Borek-32/EEE491-Spoken-Digit-Recognizer-BASYS3/hardware/homefab_mic_adc_pcb/kicad/evidence/report_views/pcb_named_nets_top_copper.png

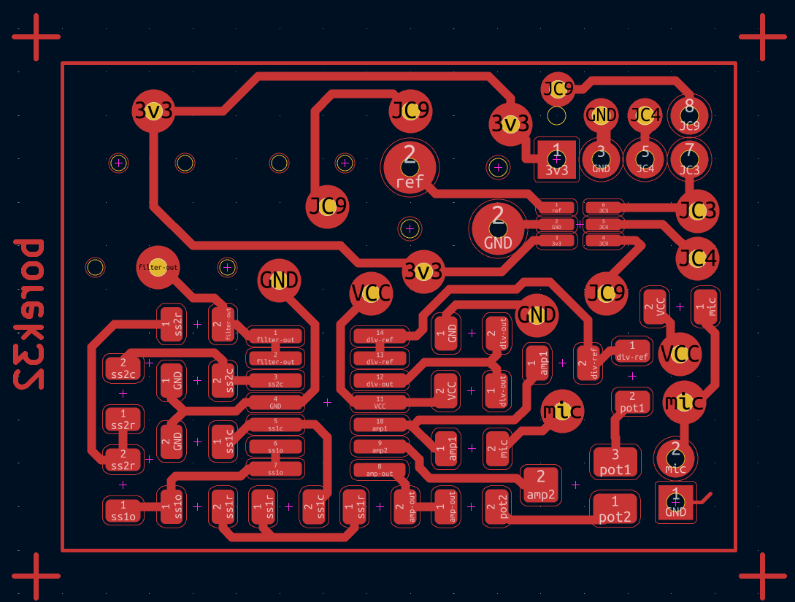
hardware/homefab_mic_adc_pcb/kicad/evidence/report_views/pcb_named_nets_top_copper.png
