Borek-32/EEE491-Spoken-Digit-Recognizer-BASYS3/hardware/homefab_mic_adc_pcb/photos/20260819_190726_operating_on_basys3.jpg

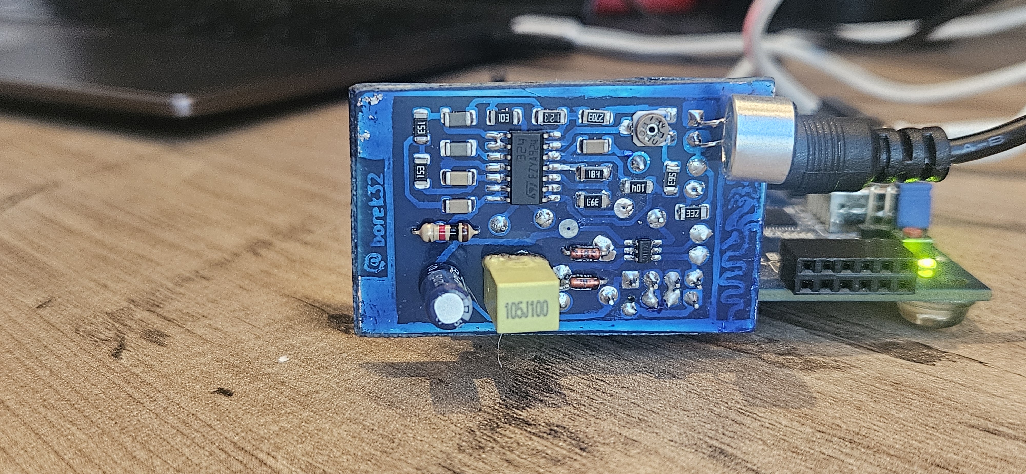
hardware/homefab_mic_adc_pcb/photos/20260819_190726_operating_on_basys3.jpg
