Borek-32/EEE491-Spoken-Digit-Recognizer-BASYS3/testbench/tb_comp.vhd

library IEEE;
use IEEE.STD_LOGIC_1164.ALL;
use IEEE.NUMERIC_STD.ALL;

-- Self-contained COMP testbench generated from verification/last_capture.mat.
-- Offline squared-Euclidean expectation: digit 9, best_ref 27, window_start 7, distance 7771316.
-- Active-start detector: first frame with sum(MEL) > max(sum(MEL))/8. Threshold 67967.
-- The three IP models below replace the Xilinx BRAM/multiplier IPs for behavioral simulation.

package tb_comp_data_pkg is
	type frame8_int_t is array (0 to 7) of integer;
	type capture_dct_t is array (0 to 62) of frame8_int_t;
	constant CAPTURE_DCT : capture_dct_t := (
		 0 => (-473, -228, 478, -880, 539, 43, 189, 385),
		 1 => (54, 77, 494, -702, 392, -226, 182, 308),
		 2 => (1374, 617, 491, -727, 62, -835, -648, -183),
		 3 => (1488, 148, 536, -544, 62, -852, -618, -310),
		 4 => (1300, 229, 81, -625, -103, -1049, -481, -194),
		 5 => (1278, 87, 206, -726, 195, -1331, -400, -251),
		 6 => (1566, -121, 271, -414, 204, -1445, -333, -294),
		 7 => (2195, -1037, -169, -797, 242, -930, -197, -243),
		 8 => (1953, -1395, -442, -644, 136, -942, 276, -369),
		 9 => (1680, -1577, -457, -553, 166, -816, 392, -420),
		10 => (1548, -1683, -520, -454, 272, -743, 436, -479),
		11 => (1387, -1852, -568, -504, 294, -798, 404, -613),
		12 => (1323, -1937, -592, -485, 327, -893, 277, -596),
		13 => (1505, -1901, -499, -424, 368, -787, 291, -405),
		14 => (1414, -1720, -521, -420, 285, -937, 383, -477),
		15 => (1522, -1866, -463, -559, 106, -994, 158, -459),
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
	port (
		clka  : in  std_logic;
		wea   : in  std_logic_vector(0 downto 0);
		addra : in  std_logic_vector(3 downto 0);
		dina  : in  std_logic_vector(127 downto 0);
		clkb  : in  std_logic;
		addrb : in  std_logic_vector(3 downto 0);
		doutb : out std_logic_vector(127 downto 0)
	);
end entity;

architecture sim of blk_mem_gen_comp_window_buf is
	type ram_t is array (0 to 15) of std_logic_vector(127 downto 0);
	signal ram : ram_t := (others => (others => '0'));
begin
	process(clka)
	begin
		if rising_edge(clka) then
			if wea(0) = '1' then
				ram(to_integer(unsigned(addra))) <= dina;
			end if;
		end if;
	end process;

	process(clkb)
	begin
		if rising_edge(clkb) then
			doutb <= ram(to_integer(unsigned(addrb)));
		end if;
	end process;
end architecture;

library IEEE;
use IEEE.STD_LOGIC_1164.ALL;
use IEEE.NUMERIC_STD.ALL;

entity mult_gen_comp_square is
	port (
		CLK : in  std_logic;
		A   : in  std_logic_vector(16 downto 0);
		B   : in  std_logic_vector(16 downto 0);
		P   : out std_logic_vector(33 downto 0)
	);
end entity;

architecture sim of mult_gen_comp_square is
	constant LATENCY : integer := 6;
	type pipe_t is array (0 to LATENCY - 1) of signed(33 downto 0);
	signal pipe : pipe_t := (others => (others => '0'));
begin
	process(CLK)
		variable prod : signed(33 downto 0);
	begin
		if rising_edge(CLK) then
			prod := resize(signed(A) * signed(B), 34);
			pipe(0) <= prod;
			for i in 1 to LATENCY - 1 loop
				pipe(i) <= pipe(i - 1);
			end loop;
			P <= std_logic_vector(pipe(LATENCY - 1));
		end if;
	end process;
end architecture;

library IEEE;
use IEEE.STD_LOGIC_1164.ALL;
use IEEE.NUMERIC_STD.ALL;
use STD.TEXTIO.ALL;
use STD.ENV.ALL;
use work.tb_comp_data_pkg.all;

entity tb_comp is
end entity;

architecture sim of tb_comp is
	constant CLK_PERIOD : time := 10 ns;
	constant DCT_DATA_LATENCY : integer := 3;
	constant MEL_DATA_LATENCY : integer := 3;
	type dct_addr_pipe_t is array (0 to DCT_DATA_LATENCY - 1) of std_logic_vector(2 downto 0);
	type mel_addr_pipe_t is array (0 to MEL_DATA_LATENCY - 1) of std_logic_vector(4 downto 0);
	signal clk          : std_logic := '0';
	signal reset_in     : std_logic := '1';
	signal clear_in     : std_logic := '0';
	signal start_in     : std_logic := '0';
	signal ready_out    : std_logic;
	signal dct_addr_out : std_logic_vector(2 downto 0);
	signal dct_data_in  : std_logic_vector(15 downto 0) := (others => '0');
	signal mel_addr_out : std_logic_vector(4 downto 0);
	signal mel_data_in  : std_logic_vector(31 downto 0) := (others => '0');
	signal selected_digit_in : std_logic_vector(4 downto 0) := "01001";
	signal selected_trial_in : std_logic_vector(2 downto 0) := "000";
	signal mode_record_in : std_logic := '0';
	signal record_out   : std_logic;
	signal flush        : std_logic := '0';
	signal flush_done   : std_logic;
	signal digit_out    : std_logic_vector(3 downto 0);
	signal valid_out    : std_logic;
	signal digit_idx3_patch : std_logic;
	signal frame_idx    : integer range 0 to 62 := 0;
	signal dct_addr_pipe : dct_addr_pipe_t := (others => (others => '0'));
	signal mel_addr_pipe : mel_addr_pipe_t := (others => (others => '0'));
	signal capture_dct_data : capture_dct_t := CAPTURE_DCT;
	signal capture_mel_data : capture_mel_t := CAPTURE_MEL;
begin
	clk <= not clk after CLK_PERIOD / 2;

	data_latency_model : process(clk)
	begin
		if rising_edge(clk) then
			dct_addr_pipe(0) <= dct_addr_out;
			for i in 1 to DCT_DATA_LATENCY - 1 loop
				dct_addr_pipe(i) <= dct_addr_pipe(i - 1);
			end loop;
			dct_data_in <= std_logic_vector(to_signed(
				capture_dct_data(frame_idx)(to_integer(unsigned(dct_addr_pipe(DCT_DATA_LATENCY - 1)))), 16));

			mel_addr_pipe(0) <= mel_addr_out;
			for i in 1 to MEL_DATA_LATENCY - 1 loop
				mel_addr_pipe(i) <= mel_addr_pipe(i - 1);
			end loop;
			mel_data_in <= capture_mel_data(frame_idx)(to_integer(unsigned(mel_addr_pipe(MEL_DATA_LATENCY - 1))));
		end if;
	end process;

	dut : entity work.COMP
		port map (
			reset_in     => reset_in,
			clock_in     => clk,
			clear_in     => clear_in,
			start_in     => start_in,
			ready_out    => ready_out,
			dct_addr_out => dct_addr_out,
			dct_data_in  => dct_data_in,
			mel_addr_out => mel_addr_out,
			mel_data_in  => mel_data_in,
			selected_digit_in => selected_digit_in,
			selected_trial_in => selected_trial_in,
			mode_record_in => mode_record_in,
			record_out   => record_out,
			flush        => flush,
			flush_done   => flush_done,
			digit_out    => digit_out,
			valid_out    => valid_out,
			digit_idx3_patch => digit_idx3_patch
		);

	stim : process
		file spec_file : text open read_mode is "../../../../verification/ref_data/tb_comp_ref.txt";
		file dct_file : text open read_mode is "../../../../verification/ref_data/tb_comp_dct_ref.txt";
			file mel_file : text open read_mode is "../../../../verification/ref_data/tb_comp_mel_ref.txt";
			file dump_file : text open write_mode is "../../../../verification/tb_output/tb_comp_output.txt";
			file record_dump_file : text open write_mode is "../../../../verification/tb_output/tb_comp_record_recall_output.txt";
		variable L : line;
		variable value_i : integer;
		variable selected_digit_v : integer;
		variable selected_trial_v : integer;
		variable valid_i : integer;
		variable record_i : integer;
		variable idx3_i : integer;
	begin
		readline(spec_file, L);
		read(L, selected_digit_v);
		read(L, selected_trial_v);
		selected_digit_in <= std_logic_vector(to_unsigned(selected_digit_v, 5));
		selected_trial_in <= std_logic_vector(to_unsigned(selected_trial_v, 3));

		for f in 0 to 62 loop
			readline(dct_file, L);
			for c in 0 to 7 loop
				read(L, value_i);
				capture_dct_data(f)(c) <= value_i;
			end loop;
		end loop;

		for f in 0 to 62 loop
			readline(mel_file, L);
			for m in 0 to 31 loop
				read(L, value_i);
				capture_mel_data(f)(m) <= std_logic_vector(to_unsigned(value_i, 32));
			end loop;
		end loop;
		wait for 1 ns;

		reset_in <= '1';
		clear_in <= '0';
		start_in <= '0';
		mode_record_in <= '0';
		flush <= '0';
			wait for 8 * CLK_PERIOD;
		wait until rising_edge(clk);
		reset_in <= '0';
		wait until rising_edge(clk);

		for f in 0 to 62 loop
			frame_idx <= f;
			wait until rising_edge(clk) and ready_out = '1';
			start_in <= '1';
			wait until rising_edge(clk);
			start_in <= '0';
			wait until rising_edge(clk) and ready_out = '0';
			wait until rising_edge(clk) and ready_out = '1';
		end loop;

		wait for 5 * CLK_PERIOD;
		if valid_out = '1' then
			valid_i := 1;
		else
			valid_i := 0;
		end if;
		if record_out = '1' then
			record_i := 1;
		else
			record_i := 0;
		end if;
		if digit_idx3_patch = '1' then
			idx3_i := 1;
		else
			idx3_i := 0;
		end if;

		write(L, valid_i);
		write(L, string'(" "));
		write(L, to_integer(unsigned(digit_out)));
		write(L, string'(" "));
		write(L, idx3_i);
		write(L, string'(" "));
		write(L, record_i);
			writeline(dump_file, L);

			assert valid_out = '1'
				report "tb_comp initial compare did not assert valid_out"
				severity failure;
			assert record_out = '0'
				report "tb_comp initial compare incorrectly asserted record_out"
				severity failure;
			assert digit_out = x"9"
				report "tb_comp initial compare did not return digit 9"
				severity failure;

			-- Focused runtime-enrollment check.  Store the same captured
			-- 16-frame active window in digit 2, trial 1, without reloading the
			-- COE or resetting the reference BRAM.
			selected_digit_in <= std_logic_vector(to_unsigned(2, 5));
			selected_trial_in <= std_logic_vector(to_unsigned(1, 3));
			mode_record_in <= '1';
			clear_in <= '1';
			wait until rising_edge(clk);
			clear_in <= '0';
			wait until rising_edge(clk);

			for f in 0 to 62 loop
				frame_idx <= f;
				wait until rising_edge(clk) and ready_out = '1';
				start_in <= '1';
				wait until rising_edge(clk);
				start_in <= '0';
				wait until rising_edge(clk) and ready_out = '0';
				wait until rising_edge(clk) and ready_out = '1';
			end loop;

			wait for 5 * CLK_PERIOD;
			assert valid_out = '1'
				report "tb_comp record run did not assert valid_out"
				severity failure;
			assert record_out = '1'
				report "tb_comp record run did not assert record_out"
				severity failure;
			assert digit_out = x"2"
				report "tb_comp record run returned the wrong enrolled digit"
				severity failure;

			write(L, string'("record "));
			write(L, 1);
			write(L, string'(" "));
			write(L, to_integer(unsigned(digit_out)));
			write(L, string'(" "));
			write(L, 1);
			writeline(record_dump_file, L);

			-- Clear only COMP's per-run state, retain the writable reference
			-- RAM, and compare the same utterance.  The newly enrolled slot has
			-- exact zero distance and must remap the result to digit 2.
			mode_record_in <= '0';
			clear_in <= '1';
			wait until rising_edge(clk);
			clear_in <= '0';
			wait until rising_edge(clk);

			for f in 0 to 62 loop
				frame_idx <= f;
				wait until rising_edge(clk) and ready_out = '1';
				start_in <= '1';
				wait until rising_edge(clk);
				start_in <= '0';
				wait until rising_edge(clk) and ready_out = '0';
				wait until rising_edge(clk) and ready_out = '1';
			end loop;

			wait for 5 * CLK_PERIOD;
			assert valid_out = '1'
				report "tb_comp recall run did not assert valid_out"
				severity failure;
			assert record_out = '0'
				report "tb_comp recall run incorrectly asserted record_out"
				severity failure;
			assert digit_out = x"2"
				report "tb_comp recall did not select the runtime-enrolled digit"
				severity failure;
			assert digit_idx3_patch = '0'
				report "tb_comp recall produced an unexpected digit-index patch"
				severity failure;

			write(L, string'("recall "));
			write(L, 1);
			write(L, string'(" "));
			write(L, to_integer(unsigned(digit_out)));
			write(L, string'(" "));
			write(L, 0);
			writeline(record_dump_file, L);

			finish;
		wait;
	end process;
end architecture;
